ljan/GBA_Emulator-by-Ryzee119-/PCB/KiCAD/GBA_EMU.sch

## KiCad design PCB/KiCAD/GBA_EMU.sch (2019-05-01, an earlier design)

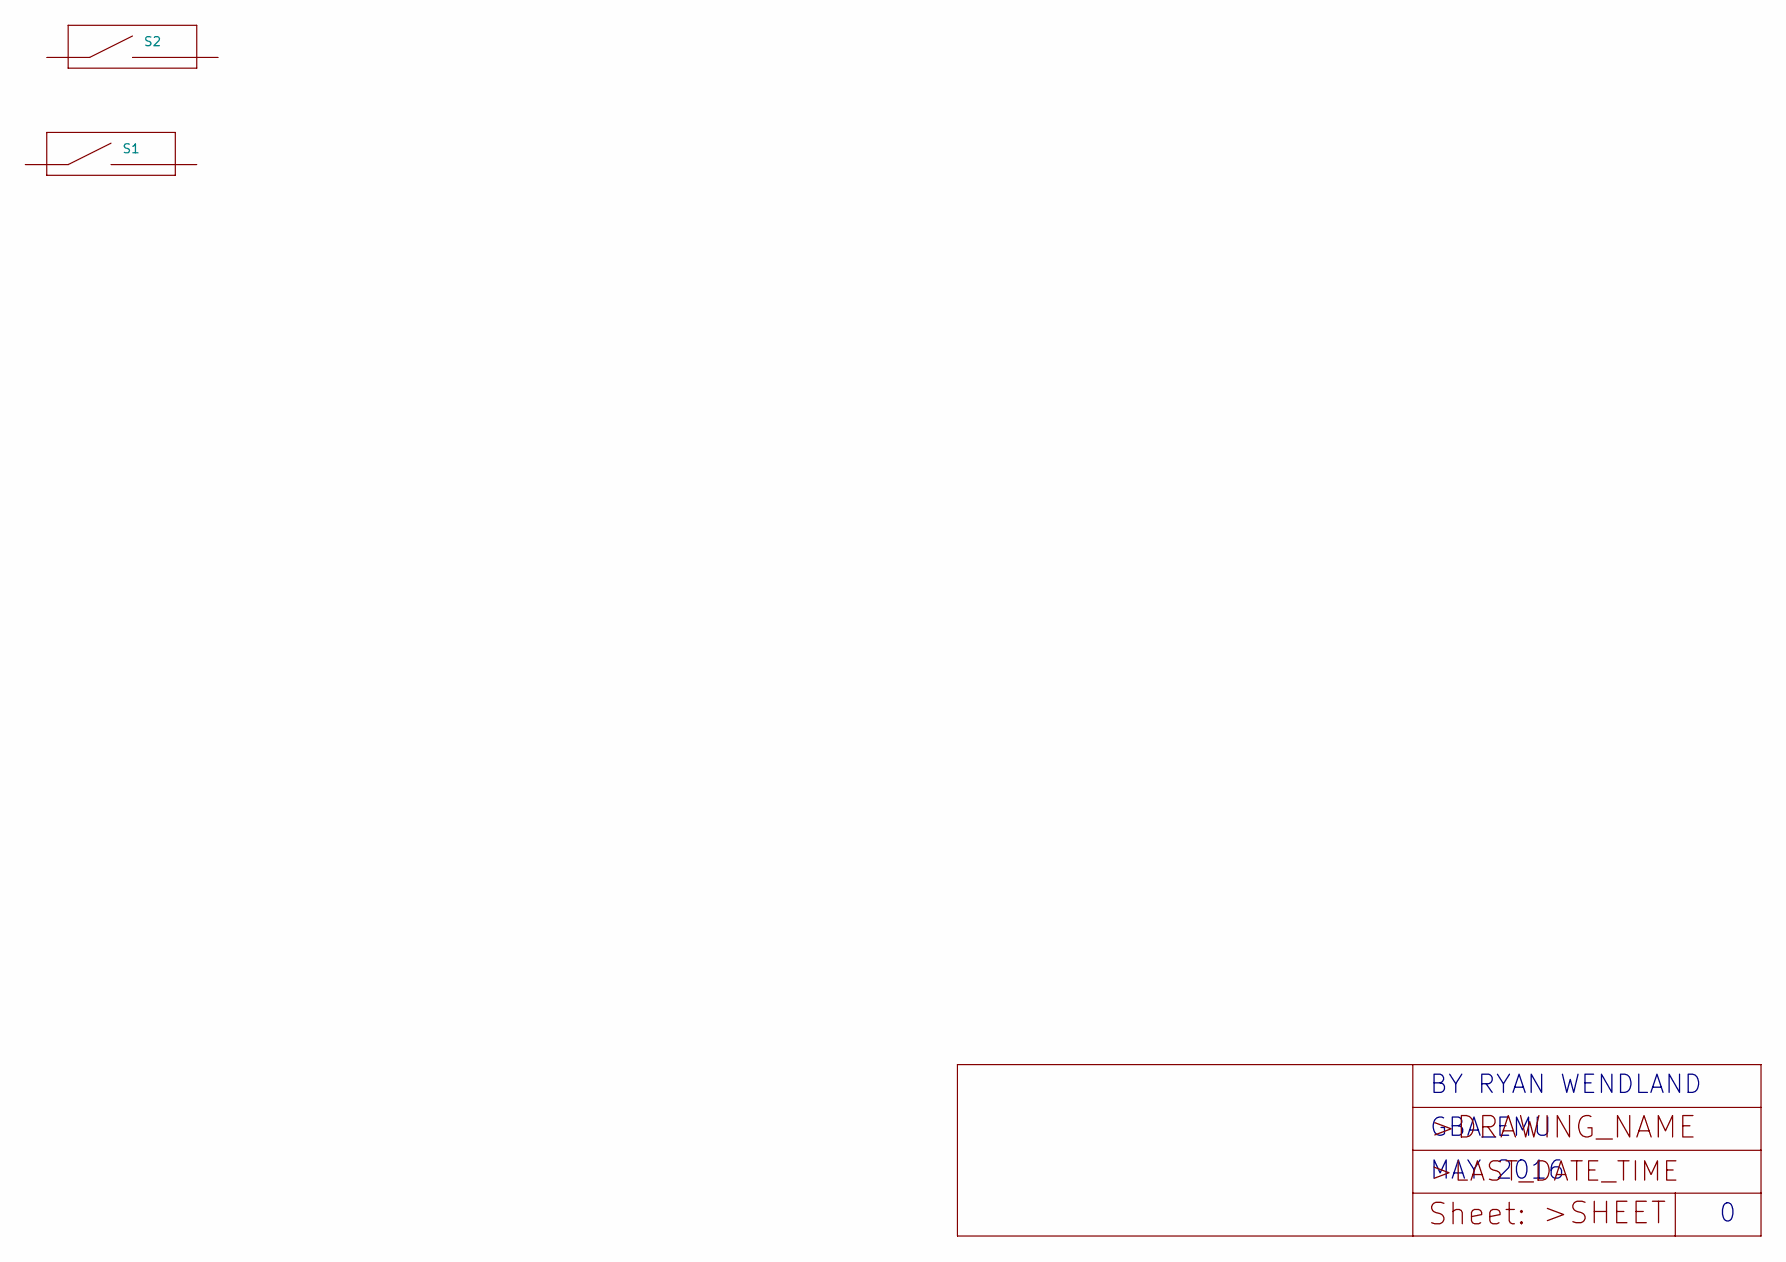
[picture p3: schematic GBA_EMU.sch]

Parts:
S1, S2: SHOULDER_BUTTON

Connections:
unnamed: S1.GND@1 (2), S1.GND@2 (2), S1.GND@3 (2)
unnamed: S2.GND@1 (2), S2.GND@2 (2), S2.GND@3 (2)

Notes on the sheet:
GBA_EMU
MAY 2016
BY RYAN WENDLAND
